GOS2022/Hardware/MB02A1/02_Prototyping_phase/PowerSupplyModule_prototype/PCB_SilkScreenTop.png

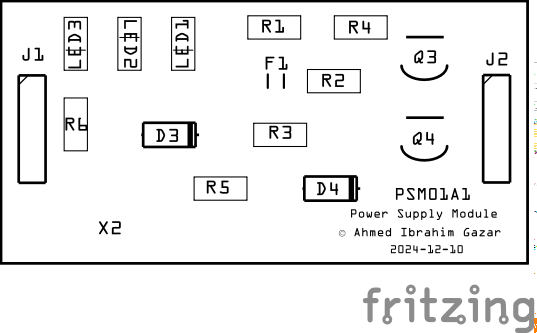
MB02A1/02_Prototyping_phase/PowerSupplyModule_prototype/PCB_SilkScreenTop.png
